100prznt/EspFieldController/docu/IMG_3661.jpeg

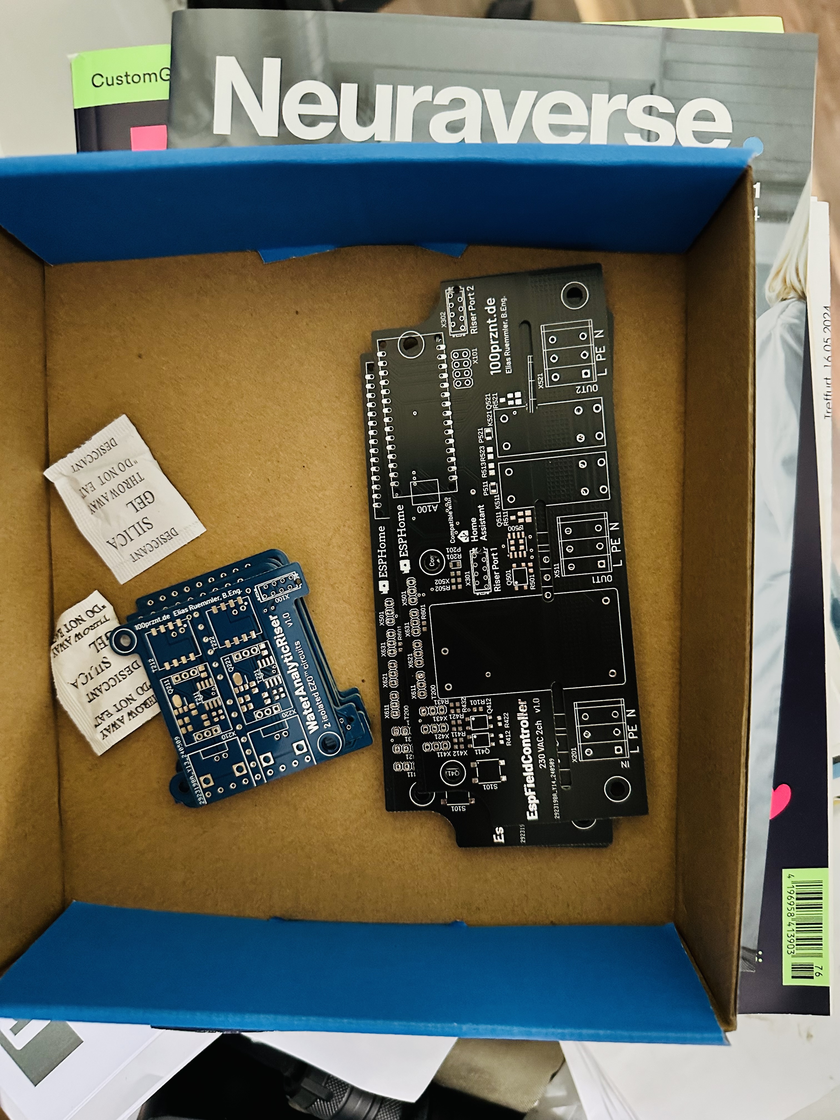
docu/IMG_3661.jpeg
