100prznt/EspFieldController/docu/IMG_4394.jpg

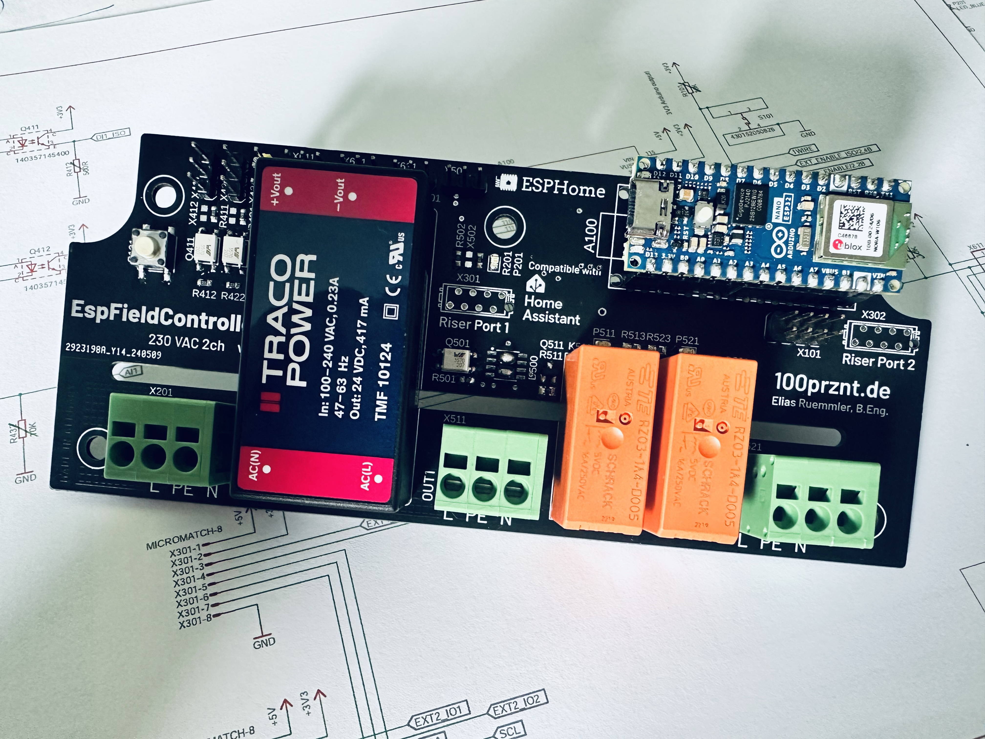
docu/IMG_4394.jpg
