100prznt/EspFieldController/production/JLCPCB_GerberView.png

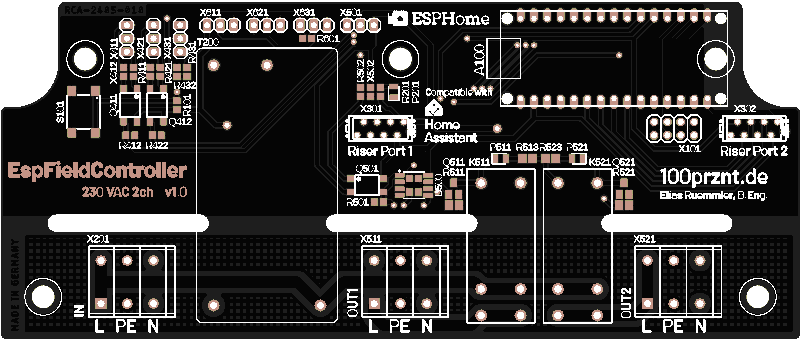
production/JLCPCB_GerberView.png
