100prznt/EspFieldController/WaterAnalyticRiser/docu/IMG_4410.jpg

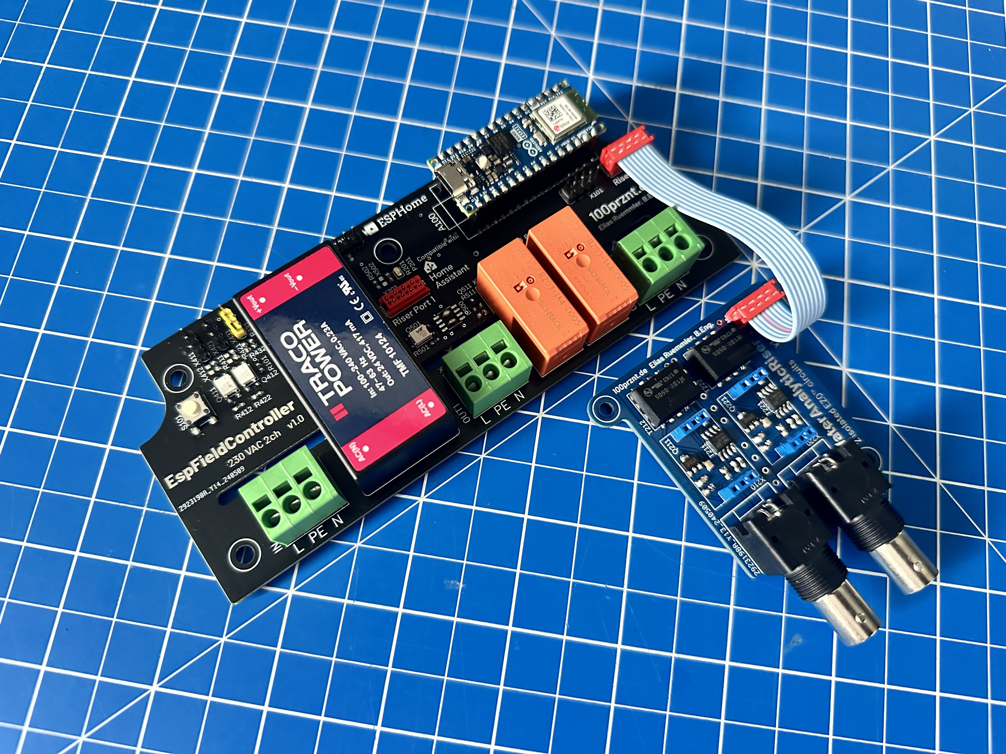
WaterAnalyticRiser/docu/IMG_4410.jpg
